fundakk/Pharus/HTML_examples/Basic_scenarios/Advanced/background.jpg

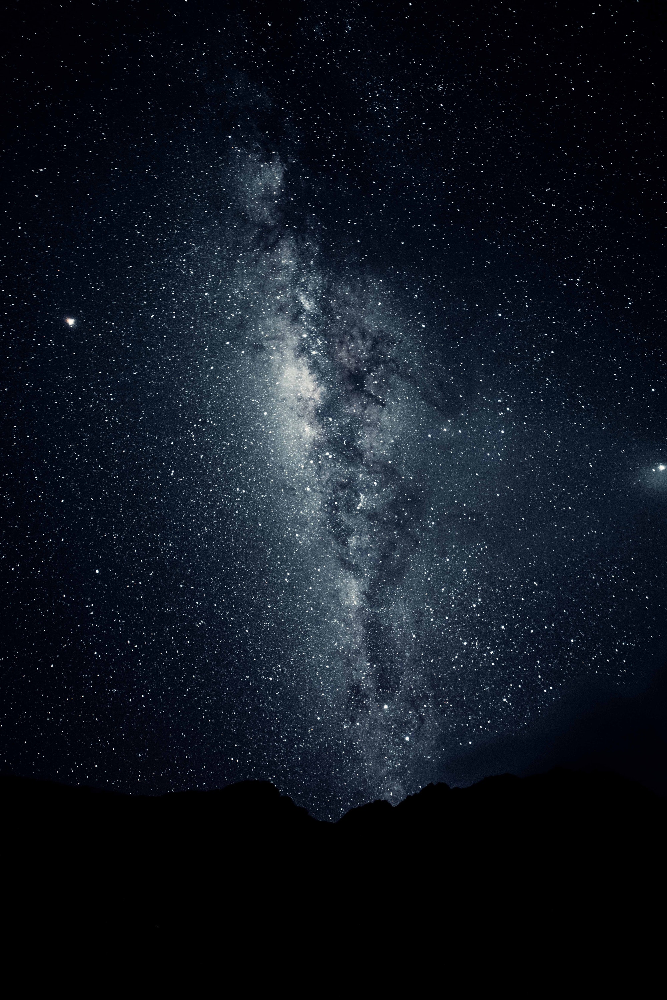
HTML_examples/Basic_scenarios/Advanced/background.jpg
