fundakk/Pharus/HTML_examples/Basic_scenarios/Advanced/image1.jpg

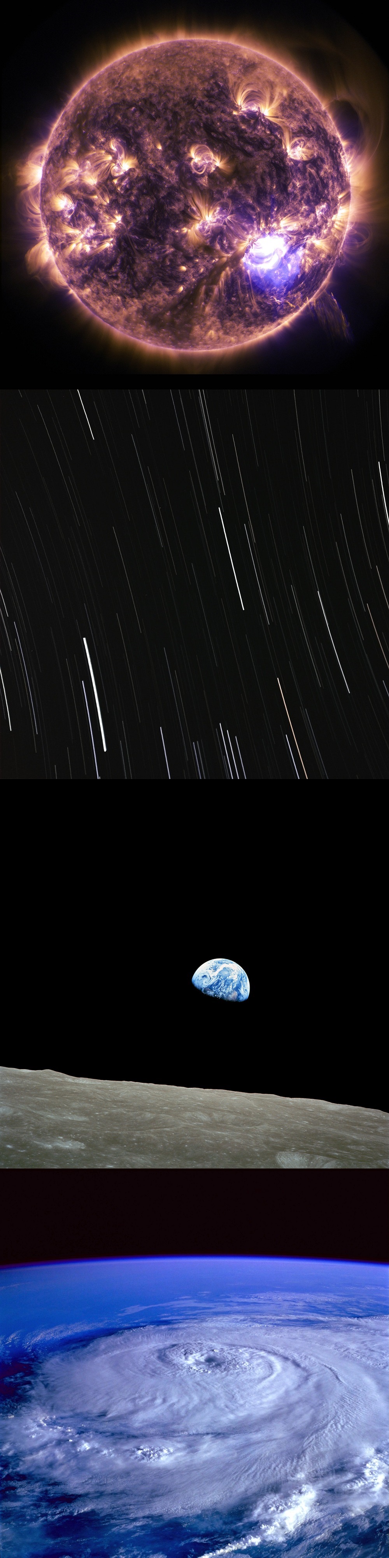
HTML_examples/Basic_scenarios/Advanced/image1.jpg
