fundakk/Pharus/HTML_examples/Basic_scenarios/Image/image1.jpg

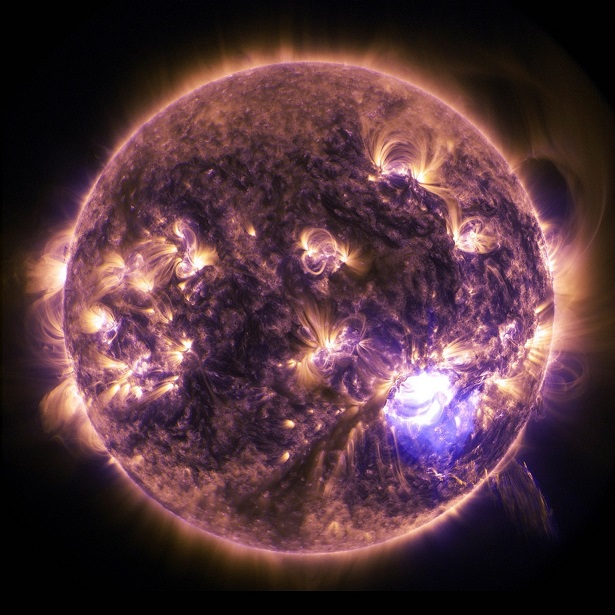
HTML_examples/Basic_scenarios/Image/image1.jpg
