fundakk/Pharus/HTML_examples/Event/image1.jpg

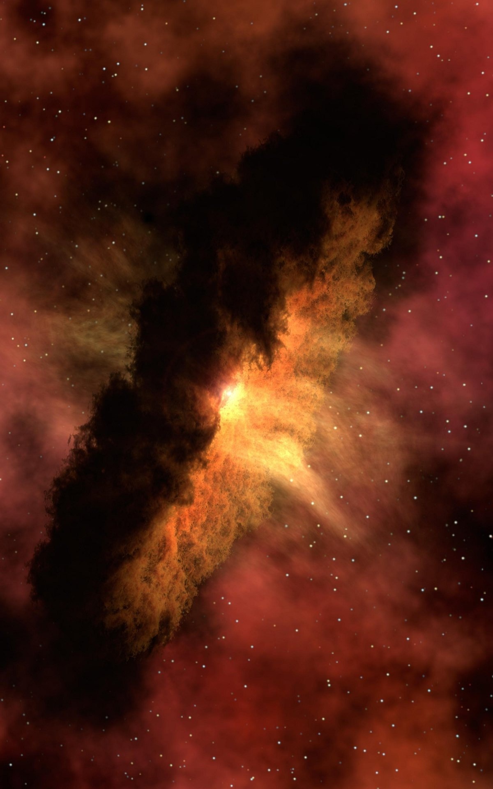
HTML_examples/Event/image1.jpg
