fundakk/Pharus/HTML_examples/Gamification/XP_collecting/image1.jpg

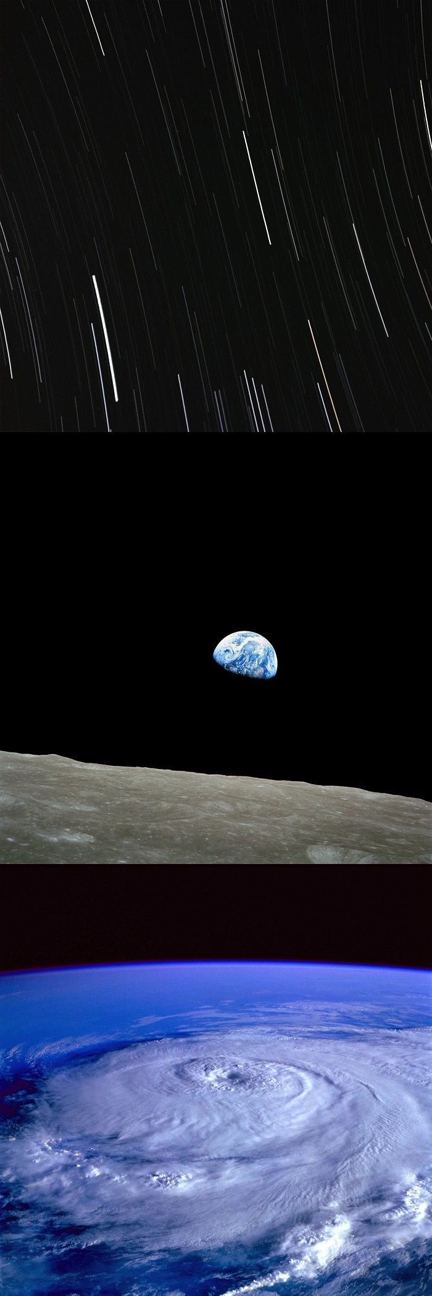
HTML_examples/Gamification/XP_collecting/image1.jpg
